shortrangetech/opendoorsim/firmware/include/opendoorsim.h

#ifndef DOORSIM_H
#define DOORSIM_H

#include <Arduino.h>

// Structs
// Fixed-size buffer sizes to avoid heap fragmentation
#define RAW_DATA_MAX 256
#define HEX_DATA_MAX 128
#define STATUS_MAX 64
#define DETAILS_MAX 128

struct CardData {
  unsigned int bitCount;
  unsigned long facilityCode;
  unsigned long cardNumber;
  char rawCardData[RAW_DATA_MAX];
  char hexData[HEX_DATA_MAX];
  int padCount;
  char status[STATUS_MAX];
  char details[DETAILS_MAX];
  int parityStatus; // -1: disabled/unchecked, 0: fail, 1: pass
  bool hasFormat;
};

struct User {
  unsigned long facilityCode;
  unsigned long cardNumber;
  char name[50];
  char flag[50];
};

struct WiegandFormat {
  unsigned int bitCount;
  unsigned int facilityCodeStart;
  unsigned int facilityCodeEnd;
  unsigned int cardNumberStart;
  unsigned int cardNumberEnd;
  int parityEvenBit;
  uint8_t parityEvenIndices[128];
  int parityEvenIndicesLength;
  int parityOddBit;
  uint8_t parityOddIndices[128];
  int parityOddIndicesLength;
};

void ISR_INT0();
void ISR_INT1();
void loadWiegandFormats();
void saveSettingsToPreferences();
void loadSettingsFromPreferences();
void saveUsersToPreferences();
void loadUsersFromPreferences();
bool checkParityBits(const WiegandFormat *format);
void saveLogToPreferences();
void loadLogFromPreferences();
const User *checkUser(unsigned long fc, unsigned long cn);
void ledOnValid();
void speakerOnValid();
void lcdInvalidCredentials();
void speakerOnFailure();
void printCardData();
unsigned long decodeFacilityCode(unsigned int start, unsigned int end);
unsigned long decodeCardNumber(unsigned int start, unsigned int end);
// Pure-binary mode: no card chunking helper
String prefixPad(const String &in, const char c, const size_t len);
String convertBinaryToHex(const String &binaryString, int &outPadCount);
void processWiegandCard();
void processCardData();
void clearDatabits();
void cleanupCardData();
bool allBitsAreOnes();
String centerText(const String &text, int width);
void printStandbyMessage();
void updateDisplay();
void printCardDataSerial();
void setupWifi();
void webServer();
void initializeDisplay();
void printDisplayText(const char *msg1, const char *msg2, const char *msg3,
                      const char *msg4);
void printDisplayRawCard();

#endif // DOORSIM_H
